Phil-CIA/Development-Station-Power-Supply/NEW_CHAT_HANDOFF.rmd

# Development Station New Chat Handoff

## Session Closeout - 2026-06-21

Project: Development Station Power Supply
Phase: Rev-B PCB review and order-prep gate

## Current Objective

Finish the Rev-B release handoff by checking the Regulator board BOM, then generate fabrication outputs if the BOM is acceptable.

## Why This Session Was Stopped

HAT Rev-B was cleaned up and now has a zero-violation DRC state after the U10 footprint fix. Regulator Rev-B still has only cosmetic DRC warnings, but the BOM on the regulator board must be checked before gerber generation.

## Verified State At Stop

- HAT Rev-B DRC: 0 violations, 0 unconnected pads, 0 footprint errors
- HAT Rev-B ERC: 0 errors, 5 warnings (AHT20/easyeda2kicad library noise only)
- Regulator Rev-B DRC: 2 warnings, 0 unconnected pads, 0 footprint errors
- Connector contract: PASS in both reduced and baseline modes

## Next Session Actions (In Order)

1. Review the Regulator Rev-B BOM before any gerber generation.
2. If BOM is acceptable, generate fabrication outputs for both Rev-B boards.
3. Record artifact paths and timestamps in handoff notes.
4. Keep KERC-04, RB-007, and J21 display power budget deferred for post-order follow-up.

## First Action Next Session

Read `HANDOFF.md`, then review the Regulator Rev-B BOM before generating fabrication outputs.

Date: 2026-06-19
Project: Development Station Power Supply
Phase: Rev-B PCB review and order-prep gate

## Current Objective

Review all recent PCB and schematic deltas across Regulator Rev-B and HAT Rev-B, then determine:
1. Must-fix before order
2. Acceptable-for-order as-is
3. Defer-to-post-order items

## Why This Session Was Stopped

User requested closeout + handoff after successful connector-contract and ERC verification passes.

## Stop Point Summary - What Was Finished

1. `scripts/verify-connector-contract.ps1` updated to match current board connector reality.
2. Required cross-board contract reduced to active design set (10 required mappings).
3. Contract verification passes in both modes:
	- reduced: PASS
	- baseline: PASS
4. Latest ERC/netlist artifacts confirmed present for both Rev-B boards.
5. Root `README.md` updated to reflect current design simplification and board readiness state.

## Verified State At Stop

- HAT Rev-B ERC: 0 errors / 0 warnings
- Regulator Rev-B ERC: 0 errors / 8 warnings (library mismatch warnings only)
- Required connector mappings: 10/10 passing in current script checks

## Files That Matter First

- `HANDOFF.md`
- `README.md`
- `scripts/verify-connector-contract.ps1`
- `hardware/kicad/dsp-regulator-hat-rev-b/DSP-Regulator-HAT-RevB.kicad_sch`
- `hardware/kicad/dsp-regulator-hat-rev-b/DSP-Regulator-HAT-RevB.kicad_pcb`
- `hardware/kicad/dsp-regulator-rev-b/DSP-Regulator-RevB.kicad_sch`
- `hardware/kicad/dsp-regulator-rev-b/DSP-Regulator-RevB.kicad_pcb`

## Next Session Actions (In Order)

1. Open both KiCad projects and run DRC with current fabrication constraints.
2. Build a disposition list for every DRC issue and major manual PCB change:
	- board
	- issue
	- severity
	- decision (fix now / accept / defer)
3. Fix all must-fix items.
4. Re-run DRC and confirm no release-blocking violations.
5. Generate fabrication outputs (gerber, drill, fab notes package).
6. Perform final order readiness review.

## Rules For Next Session

1. Keep current contract baseline intact (J1/J2 mapping and 10 required nets).
2. Do not reintroduce deprecated adjustable-channel connector requirements.
3. Keep scope on PCB release quality; avoid unrelated feature expansion.
4. Preserve verification evidence and timestamps in docs as each gate closes.

## First Action Next Session

Read `HANDOFF.md`, then run DRC on both boards and produce the must-fix/accept/defer table before any new routing edits.

## Suggested Prompt For New Chat

Continue from HANDOFF.md. Review all recent PCB changes on HAT Rev-B and Regulator Rev-B, run DRC on both boards, and produce a must-fix vs acceptable vs defer disposition list. Keep the current connector contract baseline intact and drive to fabrication output readiness.
