Phil-CIA/Development-Station-Power-Supply/NEW_CHAT_HANDOFF_SHORT.rmd

# Development Station Quick Handoff (2026-06-19)

- Session closed by user request for handoff + commit.
- Current source of truth: HANDOFF.md
- Current mission: review all PCB changes and determine must-fix vs acceptable vs defer before order.

What changed in this stop window:
- Connector contract script updated to current board mapping and reduced active signal set.
- Contract checks now pass in both reduced and baseline modes.
- ERC status confirmed:
  - HAT Rev-B: 0 errors, 0 warnings
  - Regulator Rev-B: 0 errors, 8 library warnings
- Root README updated to reflect simplified architecture and order-prep status.

Next session first move:
1. Read HANDOFF.md.
2. Run DRC on both Rev-B boards.
3. Build a disposition list: must-fix / acceptable / defer.

Paste prompt:
Continue from HANDOFF.md. Run DRC on HAT Rev-B and Regulator Rev-B, review all recent PCB edits, and classify issues into must-fix, acceptable, and defer before generating fabrication outputs.
