Phil-CIA/Development-Station-Power-Supply/HANDOFF_2026-05-31.md

# Development Station Power Supply - Handoff (2026-05-31)

## Scope
CrowPanel 4.3 in display + HAT telemetry pipeline stabilization.
Goal was to remove visible flicker while keeping fast live telemetry and usable trend charts.

## Current Baseline (Working)
1. Transport path is UART-only for HAT -> CrowPanel telemetry.
2. Display flicker is eliminated in the current rendering/timing setup.
3. Live value labels are responsive and update quickly.
4. Trend charts are re-enabled and update at a faster decimated cadence.
5. Guarded flash workflow is in use for both targets.

## Firmware State

### HAT (env: hat_c6_i2c_probe)
- File: src/i2c_scanner.cpp
- Telemetry publish loop delay is 100 ms (about 10 Hz source cadence).
- OTA policy flag remains disabled.

### CrowPanel (env: crowpanel43)
- File: crowpanel-43-bringup/include/CrowPanel43Display.h
  - RGB timing tuned for anti-tear baseline:
    - freq_write = 16 MHz
    - vsync_back_porch = 16
- File: crowpanel-43-bringup/src/main.cpp
  - kTrendSampleMs = 200
  - kChartDecimation = 2
  - kUiUpdateMinMs = 50
  - kVoltageUpdateDeadband_mV = 5
  - kCurrentUpdateDeadband_mA = 2
  - Charts enabled, secondary detail UI rate-limited separately
  - OTA policy hard-disabled in code and diagnostics

## What Was Verified
1. Repeated successful builds for HAT and CrowPanel after each tuning step.
2. Guarded flash success on:
   - HAT COM11 (ESP32-C6)
   - CrowPanel COM12 (ESP32-S3)
3. On-device behavior reported by user:
   - No flicker
   - Responsive values
   - Chart speed improved to acceptable state

## Soak Status
1. PASS (user-reported): system has been running for multiple hours with stable behavior.
2. No regressions reported during extended runtime (display stability, value updates, and chart motion remained acceptable).

## Known Pitfall and Recovery
PlatformIO package/install race can occur if multiple runs overlap.
Symptoms include missing framework files or locked firmware artifacts.

Recovery:
1. Stop stale platformio/python processes.
2. Re-run build/upload sequentially (one command at a time).
3. If framework files are missing, recover from .platformio/.cache/tmp/pkg-installing-*.

## Remaining Plan Items
1. Optional fault injection (temporary UART unplug/replug) and behavior notes.
2. Completed: high-level export hardware path planning checklist.

Procedure doc for Items 1-2:
- docs/display-project/SOAK_AND_FAULT_TEST_2026-05-31.md

Export path checklist doc:
- docs/display-project/EXPORT_PATH_CHECKLIST_2026-05-31.md

## Recommended Next Session Start
1. Read this file first.
2. Build and guarded-flash both targets once to confirm clean local state.
3. Run quick bench check:
   - value latency
   - chart motion smoothness
   - no visible flicker
4. Only tune further if user requests additional chart speed.

## Quick Commands
- HAT build: platformio run -e hat_c6_i2c_probe
- HAT flash: powershell -ExecutionPolicy Bypass -File scripts/guarded-flash.ps1 -Target hat -Action upload
- CrowPanel build: platformio run -d crowpanel-43-bringup -e crowpanel43
- CrowPanel flash: powershell -ExecutionPolicy Bypass -File scripts/guarded-flash.ps1 -Target crowpanel -Action upload
