Phil-CIA/Development-Station-Power-Supply/HANDOFF_2026-05-24.md

# WorkStation Handoff - 2026-05-24

## Session Goal
Prepare a clean restart handoff while avoiding conflicts with another active agent in the same repository.

## What Was Updated In This Session
Only these tracked files were intentionally edited in this session:

1. `docs/PROJECT_SPLIT_ISSUES_AND_PRIORITIES.md`
   - Added Issue 12: Rev A display board bring-up as a hard ordering gate.
   - Updated summary tables and redesign sequence to include that gate.

2. `platformio.ini`
   - Added/used ESP32-C6 power-supply environments:
     - `[env:hat_c6_i2c_probe]`
     - `[env:hat_c6_i2c_bridge]`
   - Multiple troubleshooting attempts were made around platform source selection.
   - Current file includes these envs and should be treated as active work-in-progress.

## Current Build Status (Power-Supply Board Path)
Target environment:
- `hat_c6_i2c_probe`

Current state:
- Build is failing.
- Latest observed error chain includes corrupted/locked PlatformIO tool packages and missing toolchain executable in path:
  - `riscv32-esp-elf-g++ is not recognized`
  - package manifest/tools metadata missing during install attempts.

Consequence:
- Upload to COM11 is blocked until PlatformIO package/toolchain state is repaired.

## Important Multi-Agent Coordination
There is another agent actively working in this repo. To avoid stepping on each other:

1. Do not mass-edit or format across the repo.
2. Before changing any file, check ownership in current session notes or chat.
3. Prefer narrow, single-file edits with a short intent note.
4. Avoid touching unrelated modified files shown in `git status`.
5. Treat `src/*.cpp` and `src/*.h` as high-collision areas unless explicitly assigned.

Suggested ownership split for restart:
- Agent A: docs, handoff, planning files (`docs/*.md`, `HANDOFF*.md`).
- Agent B: firmware/tooling execution (`platformio.ini`, `src/*`, build/upload commands).

## Safe Restart Checklist
1. Re-open workspace and run `git status --short` immediately.
2. Confirm who owns `platformio.ini` and `src/*` for this session.
3. If continuing power-supply bring-up, stay on env `hat_c6_i2c_probe` and port COM11.
4. Re-validate toolchain before upload:
   - build first,
   - upload only after successful build.

## Notes
- No commit was created in this session.
- This handoff is intended to preserve continuity without cross-agent merge conflicts.
