Phil-CIA/Development-Station-Power-Supply/HANDOFF_2026-05-27.md

# WorkStation Handoff — May 27, 2026

## Session Overview

Completed full root-cause investigation of near-zero INA3221 current readings on the HAT board. Found and confirmed the definitive hardware defect. Closed out the INA diagnostic work stream and positioned the project for CrowPanel display bring-up next.

---

## What Was Resolved This Session

### Root Cause: NMOS FETs in Wrong Orientation (Q1–Q12)

- Schematic was designed for PMOS (source-high, gate-low = ON).
- Physically installed parts are N-channel (LCSC C22469448, HL3400 clone, Vth ≈ 900mV).
- NMOS source pins connect to +5V_reg → turning on requires Vgate > 5.9V.
- 74HC595 max output = 3.3V → **FETs have never conducted via their channels**.
- The 4.74V drain node reading was body diode equilibrium, not channel conduction.
- **Fix**: Board redesign (planned). No firmware workaround is possible.

### J4 Jumper (non-schematic, must stay)

- Jumper from J4 pin 4 ("Feedback 5V") to J4 pin 7 ("+5V_reg") is the **only** power delivery path to HAT board outputs.
- Removing it without working FETs causes regulator overvoltage (FB pin floats low → duty cycle ramps to max).
- **Leave the jumper installed until the board redesign is complete.**

### INA3221 Status

| Device | Address | Channel | Shunt | Status |
|---|---|---|---|---|
| U1 | 0x40 | CH1 R13 | 200mΩ | Near-zero (FET off + jumper bypass) |
| U1 | 0x40 | CH2 R14 | 200mΩ | Near-zero |
| U2 | 0x41 | CH1 R15 | 200mΩ | Near-zero |
| U2 | 0x41 | CH2 R16 | 200mΩ | Near-zero |
| U2 | 0x41 | CH3 | ~18mΩ empirical | **✅ Working — 12V input monitor ~222mA** |
| U3 | 0x43 | CH1 R17 | 200mΩ | Near-zero |
| U3 | 0x43 | CH2 R18 | 200mΩ | Near-zero |

Only 0x41 CH3 (12V input monitor) gives valid readings. Use it as the only live telemetry source until redesign.

---

## Firmware Left On-Board (HAT)

- Environment: `hat_c6_i2c_probe`, COM11, ESP32-C6 DevKitM-1
- Source: `src/i2c_scanner.cpp`
- State: uploaded and running, scanning INA3221s in a loop
- No changes needed until hardware redesign lands

---

## Next Session Goal: CrowPanel 4.3" Display Bring-Up

The starter target already exists at `crowpanel-43-bringup/`.

### What's Already Done

- PlatformIO env `crowpanel43` targeting `esp32-s3-devkitc-1`
- UART + I2C probe baseline (0x30 board controller, 0x5D touch)
- Full RGB panel pin mapping captured in `include/CrowPanel43Display.h` (LovyanGFX Bus_RGB + GT911 touch)
- Serial command stub: `HELP`, `PING`, `STATUS`, `CMD:LABEL`, `CMD:COLOR`
- RGB panel init intentionally deferred in current baseline

### Bring-Up Plan (Ordered Steps)

**Step 1 — Verify board boots and serial is healthy**
- Build and flash `crowpanel43` env
- Confirm serial output at 115200 baud
- Run `STATUS` command → should respond `board=0x30:ok touch=0x5D:ok`

**Step 2 — Enable RGB panel init**
- Instantiate `CrowPanel43Display` in `main.cpp`
- Call `display.init()` and fill screen with a solid color
- Confirm display lights up (no backlight glitch, correct colors)
- Note: backlight on CrowPanel 4.3 is controlled via the 0x30 board controller over I2C

**Step 3 — Add LVGL layer**
- Add `lvgl` library to `crowpanel-43-bringup/platformio.ini`
- Wire LovyanGFX as the LVGL display driver (flush callback)
- Wire GT911 touch as LVGL input device
- Render a minimal "hello" label to prove the stack end-to-end

**Step 4 — Basic telemetry UI**
- Display live 12V input current (INA3221 0x41 CH3) read over UART from the HAT board
- Lay out a simple bar or numeric widget

### Key Hardware Facts for Next Session

| Item | Value |
|---|---|
| Display | Elecrow CrowPanel Advance 4.3", 800×480 RGB, GT911 touch |
| MCU | ESP32-S3 (on-board) |
| Board controller I2C | 0x30 |
| Touch I2C | 0x5D (GT911) |
| PlatformIO env | `crowpanel43` in `crowpanel-43-bringup/platformio.ini` |
| RGB pixel clock | 21 MHz (freq_write in CrowPanel43Display.h) |
| PSRAM | Required (BOARD_HAS_PSRAM build flag already set) |

### Files to Read First (Next Session)

1. `crowpanel-43-bringup/README.md`
2. `crowpanel-43-bringup/include/CrowPanel43Display.h` — full pin map
3. `crowpanel-43-bringup/src/main.cpp` — current baseline firmware
4. `crowpanel-43-bringup/platformio.ini`
5. `docs/display-project/README.md` — display project context

---

## Session Reference Files

- Full hardware findings: `/memories/repo/hat-board-bringup-findings.md`
- HAT board INA3221 firmware: `src/i2c_scanner.cpp`
- HAT env: `hat_c6_i2c_probe` (COM11, ESP32-C6)
- **Do not use COM4** — that is the separate esp32dev main board

---

## No Commits Created This Session

All changes remain as working files. No git operations were performed.
