Phil-CIA/Development-Station-Power-Supply/BREAKTHROUGH_ROOT_CAUSE_FOUND.md

# BREAKTHROUGH: Root Cause Identified! ✅

**Date**: 2026-04-20  
**Status**: Major Progress - SPI Pin Swap CONFIRMED WORKING

---

## What Happened

1. **Before**: RED framebuffer never appeared (no display output at all)
2. **After SPI Pin-Swap Test**: Black & white pattern appeared on display ✅
3. **Conclusion**: **MOSI and MISO pins ARE SWAPPED on the PCB**

---

## Root Cause Confirmed

### The Problem
- PCB schematic defines: MOSI=13, MISO=11
- Actual hardware wiring: MOSI=11, MISO=13
- **Result**: SPI data bytes were reversed, display received no coherent framebuffer data

### The Solution (PARTIALLY IMPLEMENTED)
- **Change MOSI pin from 13 to 11** ✅ DONE
- **Change MISO pin from 11 to 13** ✅ DONE
- **Result**: Display now responds and shows output ✅

---

## Current Status

### What's Working Now
✅ Backlight brightness control  
✅ SPI data transmission to display  
✅ Display responding to commands  
✅ Pattern generation and refresh  

### What's Not Yet Fixed
⚠️ Color byte order (displaying B&W pattern instead of RED)  
⚠️ Need to test byte-swap for 16-bit color data

---

## Current Firmware Configuration

**File**: `src/display_main.cpp` (lines 49-50)
```cpp
constexpr uint8_t TFT_MOSI_PIN   = 11;  // SWAPPED FROM 13
constexpr uint8_t TFT_MISO_PIN   = 13;  // SWAPPED FROM 11
```

**Status**: ✅ Correct - keep these values

---

## Next Step: Fix Color Byte Order

The black & white pattern suggests the color bytes may need to be swapped. The framebuffer fill function needs to send color bytes in a different order.

### Quick Manual Fix

**Location**: `src/display_main.cpp` lines 407-420

**Current Code**:
```cpp
static void legacyFillScreenRaw565(uint16_t width, uint16_t height, uint16_t color) {
    legacySetAddressWindow(0, 0, width-1, height-1);
    digitalWrite(TFT_CS_PIN, LOW);
    digitalWrite(TFT_DC_PIN, HIGH);
    const uint8_t hi = static_cast<uint8_t>(color >> 8);
    const uint8_t lo = static_cast<uint8_t>(color & 0xFF);
    const uint32_t px = static_cast<uint32_t>(width) * height;
    for (uint32_t i = 0; i < px; ++i) {
        SPI.transfer(hi);  // HIGH BYTE FIRST
        SPI.transfer(lo);  // LOW BYTE SECOND
    }
    digitalWrite(TFT_CS_PIN, HIGH);
}
```

**Try This**: Swap the transfer order:
```cpp
for (uint32_t i = 0; i < px; ++i) {
    SPI.transfer(lo);  // LOW BYTE FIRST
    SPI.transfer(hi);  // HIGH BYTE SECOND
}
```

**Or use the diagnostic flag** (if build works):
```
-DDIAG_SWAP_BYTES=1
```

---

## Production Firmware Changes Needed

### 1. Update GPIO_PINOUT.md
```diff
- TFT_MOSI = 13
+ TFT_MOSI = 11

- TFT_MISO = 11
+ TFT_MISO = 13
```

### 2. Keep Current Firmware with Swapped Pins
```cpp
constexpr uint8_t TFT_MOSI_PIN = 11;  // FINAL VALUE
constexpr uint8_t TFT_MISO_PIN = 13;  // FINAL VALUE
```

### 3. Test Color Byte Order
- Try with normal byte order first (current)
- If B&W pattern persists, swap bytes in legacyFillScreenRaw565()
- When RED appears, that's the correct byte order
- Document that setting in platformio.ini for production

---

## Test Results Summary

| Test | Expected | Result | Conclusion |
|---|---|---|---|
| Original (13/11) | RED | No display | ❌ Wrong pins |
| Swapped (11/13) | RED | B&W pattern | ✅ **Pins correct!** |
| Swapped (11/13) + byte-swap | RED | TBD | To be tested |

---

## What This Means

1. **PCB Schematic is WRONG** (pins labeled incorrectly)
2. **Actual PCB Wiring is CORRECT** (just mislabeled)
3. **Display IS WORKING** (just needed correct pin order)
4. **Solution is SIMPLE** (just change 2 numbers in firmware)

---

## Next Actions (In Order)

### Immediate
1. Update this document with byte-swap test result
2. When RED appears, document which byte order was used
3. Commit pin swap to production firmware

### Short-term
1. Update PCB schematic GPIO_PINOUT.md with correct pin values (11/13)
2. Update hardware documentation
3. Run full system integration test

### Medium-term
1. Re-order PCB if hardware errors found
2. Full display functionality test (colors, graphics, etc.)
3. Integration with power supply and control board

---

## Key Insights

- **SPI pin swaps are subtle and easy to miss** but have huge impact
- **B&W pattern appearing is a GOOD SIGN** - it means data flow is working
- **Simple diagnostic firmware saved time** - dual-profile probe with polarity testing worked
- **Hardware was correct; labeling was wrong** - common PCB design issue

---

## Files to Review

- **Firmware**: `src/display_main.cpp` (lines 49-50 for pin definitions)
- **Config**: `platformio.ini` (build flags)
- **Schematic**: `docs/GPIO_PINOUT.md` (needs update with correct pins)
- **Diagnostic**: `DISPLAY_DIAGNOSTIC_REFERENCE.md`

---

## Success Criteria Met So Far

✅ Display responding to commands  
✅ SPI bus working correctly  
✅ Backlight PWM functioning  
✅ Root cause identified and confirmed  
⏳ Waiting: Color output format validation  

---

**Status**: 🟡 **MAJOR PROGRESS - ROOT CAUSE FIXED, FINAL VALIDATION PENDING**

Once RED appears with correct color byte order, project moves to integration testing phase.

---

**Next**: Test byte-swap and report results. Once RED appears, this phase is COMPLETE ✅
