Phil-CIA/Development-Station-Power-Supply/BYTE_SWAP_FIRMWARE_UPLOADED.md

# ✅ Byte-Swap Diagnostic Firmware UPLOADED

**Status**: Firmware successfully built and uploaded to COM9  
**Timestamp**: 2026-04-20 (After breakthrough discovery)  
**Build Time**: 67.67 seconds  
**Upload Port**: COM9 (ESP32-C6)  

---

## What Was Uploaded

### Configuration
- **Profile**: ILI9488 RGB666 init table (PANEL_CTRL_ILI9488)
- **SPI Pins**: MOSI=11, MISO=13 ✅ (SWAPPED from original schematic)
- **Byte Order**: **LO-BYTE FIRST** (DIAG_SWAP_BYTES=1) - NEW TEST
- **DC Polarity**: Normal (DIAG_INVERT_DC=0)
- **CS Polarity**: Normal (DIAG_INVERT_CS=0)

### What This Means
The firmware will now send 16-bit color data with **reversed byte order**:
- Instead of: Hi-byte → Lo-byte
- Now sending: **Lo-byte → Hi-byte**

This is testing the hypothesis that the display expects the opposite byte order than currently being sent.

---

## Expected Behavior After Upload

### Boot Sequence
1. ESP32-C6 performs hardware reset via GPIO19 (TFT_RST_PIN)
2. Backlight ramps brightness: 0→255 over ~5 seconds
3. Display controller (ST7796 or ILI9488) initializes
4. Serial output shows diagnostic boot messages:
   ```
   [BOOT] Display Probe Starting...
   [INIT] SPI Bus configured: SCLK=12, MOSI=11, MISO=13, CS=10
   [INIT] Display controller initialized (ILI9488 RGB666)
   [DIAGNOSTIC] Byte-swap mode ENABLED (Lo-byte first)
   [STATUS] Ready - filling screen with RED (0xF800)
   ```

### Screen Output
- **If byte-swap is CORRECT**: Screen fills with **RED** ✅
- **If byte-swap is WRONG**: Screen shows **B&W pattern** (same as before)

---

## Critical Test: Cold Power-Cycle Required

**⚠️ DO NOT RELY ON SOFT RESET - MUST PERFORM HARD POWER-CYCLE**

### Steps
1. Unplug the display module from the connector (USB-C or XT90 connector)
2. Wait **5+ seconds** for capacitors to discharge
3. Replug the display module
4. Observe screen output immediately
5. Check serial output on COM9 at 115200 baud

---

## What To Report

### If RED Appears ✅
```
Report: "RED framebuffer now appears after byte-swap fix!"
Action: This is the root cause found - lo-byte-first byte order is CORRECT
Next: Prepare production firmware with byte-swap as permanent setting
```

### If B&W Pattern Continues
```
Report: "B&W pattern persists with byte-swap enabled"
Action: Hypothesis needs refinement - byte order may not be the issue
Next: Test alternative theories (RGB666 format, COLMOD register, control sequence)
```

### If No Display Output
```
Report: "Display completely dark (no backlight, no pattern)"
Action: Possible firmware upload issue - retry or check COM9 connection
Next: Verify upload logs in pio_upload_display_board.log
```

---

## Firmware Build Details

### Build Command Used
```bash
cd "c:\Users\user\Esp32 projects VScode\WorkStation"
rm -r .pio .platformio  # Full cache clear
platformio run -e display_board -t upload --upload-port COM9
```

### Build Configuration (platformio.ini)
```ini
[env:display_board]
platform = espressif32 (55.3.38)
board = esp32-c6-devkitm-1
framework = arduino
upload_port = COM9
upload_speed = 460800
monitor_speed = 115200

build_flags =
    -DDIAG_SWAP_BYTES=1      # ← ACTIVE: Lo-byte-first color order
    -DDIAG_INVERT_DC=0       # Normal DC polarity
    -DDIAG_INVERT_CS=0       # Normal CS polarity
    -DPANEL_CONTROLLER=PANEL_CTRL_ILI9488  # ILI9488 RGB666 init
    -DMINIMAL_TFT_ONLY=1     # Raw SPI mode

lib_deps =
    moononournation/GFX Library for Arduino @ ^1.6.5

build_src_filter = +<display_main.cpp>
```

### Compilation Results
- ✅ All GFX library files compiled successfully
- ✅ No errors after full .pio/.platformio cache clear
- ✅ Binary size: ~333KB (25.5% of 1.3MB flash)
- ✅ RAM usage: 5.0% (16448/327680 bytes)

### Upload Results
- ✅ Connected to ESP32-C6 on COM9
- ✅ firmware.bin transferred successfully
- ✅ Hard reset via RTS pin trigger
- ✅ Upload completed in 67.67 seconds

---

## Files Modified for This Build

### `platformio.ini`
- Line 21: `-DDIAG_SWAP_BYTES=1` (was 0, now enabled)

### `src/display_main.cpp`
- Lines 407-420: `legacyFillScreenRaw565()` function includes:
  ```cpp
  #if DIAG_SWAP_BYTES
      SPI.transfer(lo);   // Lo-byte FIRST
      SPI.transfer(hi);   // Hi-byte SECOND
  #else
      SPI.transfer(hi);   // Hi-byte first
      SPI.transfer(lo);   // Lo-byte second
  #endif
  ```

---

## Previous Firmware Versions

| Version | Config | Result | Status |
|---|---|---|---|
| v1 (Original pins 13/11) | Normal pinout | No display | ❌ |
| v2 (Swapped pins 11/13) | Normal byte order | B&W pattern | ⚠️ Working bus |
| v3 (Swapped pins 11/13) | **LO-BYTE-FIRST** | **TBD** | 🟡 **TESTING NOW** |

---

## Next Steps Upon Observation

### Immediate (After you report)
1. Interpret RED vs B&W vs dark result
2. If RED: Document byte-swap as final fix
3. If B&W: Prepare alternative tests (RGB666 format, endianness)
4. If dark: Investigate upload or connection issues

### Short-term (When byte-swap fixed)
1. Update production firmware with `DIAG_SWAP_BYTES=1` as default
2. Commit byte-swap setting to repository
3. Update GPIO_PINOUT.md with correct pin values (11/13)
4. Run full color cycle test (Red, Green, Blue, White, Black)

### Long-term
1. Integration with power supply control board
2. Full system functional testing
3. PCB revision documentation (if hardware changes needed)

---

## Diagnostic Mode Summary

This firmware is in **DIAGNOSTIC MODE** - it's designed to isolate specific hardware issues:

- ✅ SPI communication working (B&W pattern proved this)
- ✅ Backlight PWM functional
- ✅ Display responding to commands
- ⏳ Color format byte order under investigation
- ⏳ RGB565 color accuracy pending

Once RED appears with byte-swap, diagnostic phase is COMPLETE and production bring-up begins.

---

## Contact / Status

**Who uploaded**: Agent (autonomous)  
**When**: 2026-04-20 (after successful ROOT CAUSE identification)  
**Why**: Testing final hypothesis before moving to production firmware  
**Expected observation time**: Within 5 minutes of power-cycle  

**Status Dashboard**:
- 🟡 Firmware uploaded and waiting for user observation
- 🟡 Byte-swap test active
- 🟡 Display module ready for cold power-cycle
- 🟡 Serial output monitoring ready on COM9

---

**NEXT ACTION**: Power-cycle the display module and observe. Report result to start final phase of bring-up! 🚀
