Phil-CIA/Development-Station-Power-Supply/docs/DEV_STATION_HANDOFF_2026-09-23.md

**AW9523 Bringup Handoff**

Date: 2026-09-23

- **Summary**: Continued bring-up of AW9523 GPIO/LED driver on the Blue Pill helper path. Migrated control to the Adafruit AW9523 driver, enforced GPIO push-pull at boot, added diagnostics and bench commands (including Q9-specific diagnostics), and validated a working build/upload flow using PlatformIO's penv.

- **Changed Files**:
  - **Code**: [stm32-bluepill-bringup/src/main.cpp](stm32-bluepill-bringup/src/main.cpp)
  - **Build**: [stm32-bluepill-bringup/platformio.ini](stm32-bluepill-bringup/platformio.ini)

- **Key Symbols / Routines**:
  - `aw95xxBootInit()` — enforces LEDMODE, GCR push-pull, and `CFG_P0` policy at boot.
  - `aw95xxEnsureGpioPushPull()` — checks/sets GCR and LEDMODE registers.
  - `aw95xxWriteP0Mask()` / `aw95xxSetP0MaskOutputMode()` — set outputs for P0.0/P0.1/P0.5.
  - `Q9DIAG` / `runQ9ElectricalDiagnostic()` — bench diagnostic sequence to detect external clamping on P0.5.

- **How to build & upload (known-good)**:
  - Use PlatformIO penv to avoid host Python 3.14 incompatibility:

    ```powershell
    & "%USERPROFILE%\.platformio\penv\Scripts\platformio.exe" run -d stm32-bluepill-bringup -e bluepill_f103c8
    & "%USERPROFILE%\.platformio\penv\Scripts\platformio.exe" run -d stm32-bluepill-bringup -e bluepill_f103c8 -t upload
    ```

- **Serial/command checks to run in next session** (run from the Blue Pill serial console at 115200):
  - `AWPROBE` — confirm AW9523 ACK at 0x58
  - `AWMODE` — print GCR/CFGs/LEDMODE; expect GCR=push-pull and LEDMODE P0/P1 = 0xFF
  - `Q9DIAG` — run the Q9 diagnostic and capture `aw95xx diag` outputs
  - `Q9ON` / `Q9OFF` — toggle Q9 path and observe `QSTATE` and scope at AW P0.5 and Q9 gate
  - `INANOW` / `INAPROBE` — optional INA readings for rail-state correlation

- **Expected Responses / Bench checks**:
  - `AWMODE` should show: GCR=0x?? (port=push-pull), `LEDMODE_P0`/`P1` = 0xFF, `CFG_P0` = 0xC0 (P0.0..P0.5 outputs)
  - `Q9DIAG` should show `input latch` following output when AW drives high (if external clamp present, diagnostic warns)
  - On oscilloscope: AW P0.5 should actively drive high to ~3.3V when commanded; gate node should move accordingly unless there is a hardware clamp

- **Known issues / notes**:
  - PlatformIO on host Python 3.14 required using the penv executable (documented in repo memory). Do not run `py -m platformio` with system Python 3.14 for library installs.
  - One transient OpenOCD init error occurred during upload historically; retry succeeded. Do not assume intermittent connect failures indicate firmware problems.
  - The code now uses Adafruit AW9523 APIs; avoid mixing manual register writes and library APIs without confirming semantics.

- **Flash safety**: Verify target and COM/adapter before uploading. Do not 'COM port shop' — follow the guarded upload tasks in VS Code tasks.

- **Next actions for the incoming engineer / next chat**:
  - Run the serial checks above and paste the `AWMODE` and `Q9DIAG` outputs into the next chat.
  - If AW P0.5 reads as expected but downstream gate doesn't move, perform powered-off resistance checks and isolate the gate path (measure continuity to ground/3.3V, check diode/clamp parts).
  - If AW doesn't respond at 0x58, check I2C wiring and pull-ups on the board, then run `AWPROBE` and share logs.

Prepared by: Development Station agent — handoff snapshot saved to repo.

---

## Session Scope Update (2026-09-23): Range MOSFET Control

This session is now defined as **range MOSFET control bring-up**.

### Goal

Determine whether firmware has direct command control over MOSFET gate paths and whether the target MOSFET paths respond electrically.

### Added command coverage (Blue Pill AW9523 path)

- `Q1ON` / `Q1OFF` -> AW9523 `P0.2` (`ESP- GPIO 5V Low`) for `Q1/Q7` gate path.
- `Q2ON` / `Q2OFF` -> AW9523 `P0.1` (`ESP- GPIO 5V Hi`) for `Q2/Q8` gate path.
- `Q4ON` / `Q4OFF` -> AW9523 `P0.4` (`ESP- GPIO 3V3 Low`) for `Q4/Q10` gate path.
- `Q5ON` / `Q5OFF` -> AW9523 `P0.3` (`Channel 3 Hi-Range`) for `Q5/Q11` gate path.
- Existing retained:
  - `Q3ON` / `Q3OFF` -> `P0.0` (Q3 path)
  - `Q9ON` / `Q9OFF` -> `P0.5` (Q9 path)
  - `Q39ON` / `Q39OFF` and `Q612ON` / `Q612OFF` pair-level tests

### Recommended bench order for gate-control verification

1. `AWPROBE`
2. `AWMODE`
3. `QSTATE` (baseline capture)
4. `Q1OFF`, `QSTATE`, then `Q1ON`, `QSTATE`, then `Q1OFF`, `QSTATE`
5. `Q2OFF`, `QSTATE`, then `Q2ON`, `QSTATE`, then `Q2OFF`, `QSTATE`
6. Repeat pattern for `Q3`, `Q4`, `Q5`, and `Q9` paths
7. Run `INARAILS` after each ON/OFF transition where current-path response is expected

### What to record per step

- `QSTATE` decode (P0 output bit and direction)
- Scope measurement at AW pin and at MOSFET gate
- INA directional changes when applicable
- Any mismatch where AW output toggles but gate node does not move (possible clamp/loading issue)

---

## Session Closeout (2026-09-23): Range MOSFET Control

### Final verdict

**PASS**: firmware control over the range MOSFET gate paths is confirmed good enough to close this session.

### What was validated live

1. Blue Pill firmware uploaded and verified by ST-Link (`Programming Finished`, `Verified OK`, target reset).
2. AW9523 control path confirmed active at `0x58` (`AWPROBE` ACK).
3. Direct gate-path commands were exercised and read back with matching output and input latch state (`want/out/in` aligned) for:
  - `Q1ON/Q1OFF` -> `P0.2` (`Q1/Q7` path)
  - `Q2ON/Q2OFF` -> `P0.1` (`Q2/Q8` path)
  - `Q3ON/Q3OFF` -> `P0.0`
  - `Q4ON/Q4OFF` -> `P0.4` (`Q4/Q10` path)
  - `Q5ON/Q5OFF` -> `P0.3` (`Q5/Q11` path)
  - `Q9ON/Q9OFF` -> `P0.5`
4. Consolidated OFF->ON->OFF sweep completed for all six paths with `QSTATE` and `INARAILS` captures.
5. Directional INA response observed on expected paths (notably Q2, Q4, Q5), and all paths returned to baseline OFF state (`p0=0x00`) at end of run.

### Closure statement

For current bring-up purposes, this closes the **range MOSFET control** objective. Treat command-path control as validated and move to calibration work in the next session.

---

## Next Session Start: Calibration

Use this as the opening scope for the next chat:

1. Confirm bench baseline (`AWPROBE`, `QSTATE`, `INARAILS`).
2. Keep range paths in known-safe OFF baseline unless a calibration step requires a specific state.
3. Begin calibration sequence (rail/telemetry calibration workflow) and capture coefficients/results.
4. Log final calibration outputs and pass/fail gates in a new handoff entry.
5. Follow `docs/CALIBRATION_WORKFLOW_2026-09-23.md` as the active recovered-and-updated calibration procedure.

Suggested next-session opener text:

"Range MOSFET control session is closed PASS on 2026-09-23. Start calibration session from Blue Pill baseline state with AW9523 verified at 0x58 and all range paths OFF."
