Phil-CIA/Development-Station-Power-Supply/docs/DEV_STATION_HANDOFF_2026-07-29.md

# Dev Station Handoff - 2026-07-29

## Session Closeout

Range-switch driver rework moved from concept to validated schematic/netlist state on HAT Rev-B using LM74502H high-side NMOS drivers.

Primary goal for this session was to resolve the prior ambiguous Vgs behavior on high-side back-to-back NMOS range switches by introducing a proper high-side gate driver topology.

## What Was Completed

1. Implemented LM74502H-based gate drive topology for all four range-switch channels.
2. Confirmed OV divider strategy per channel (R1/R2 style implemented as 390k/100k where shown).
3. Confirmed VCAP charge-pump capacitor presence per channel and net connectivity.
4. Verified U6/U8/U13/U14 channel consistency in netlist (VS, VCAP, GATE, SRC, OV, EN/UVLO).
5. Confirmed ERC export is clean.
6. Created timestamped backup snapshot of key artifacts.

## Verified State At Stop

- HAT Rev-B ERC: 0 errors, 0 warnings.
- Four LM74502H channels pass netlist-level connectivity checks:
  - VS on +5V_Boot
  - VCAP capacitor connected VCAP-to-VS
  - OV divider connected to VS and GND with OV at divider midpoint
  - GATE output isolated from MCU logic nets
  - SRC tied to common source node of each back-to-back NMOS pair
- Backup created at:
  - hardware/kicad/dsp-regulator-hat-rev-b/backups/20260729-042040/
  - includes:
    - DSP-Regulator-HAT-RevB.kicad_sch
    - DSP-Regulator-HAT-RevB.net
    - ERC.rpt

## Important Notes For Next Session

1. Netlist validation is complete; physical layout proximity still matters.
2. Ensure each LM74502H has local VS-to-GND bypass placement close to the IC in PCB layout (in addition to VCAP-to-VS cap).
3. Confirm zener polarity per channel at schematic symbol orientation level:
   - Cathode to gate net
   - Anode to source net

## Open Issue: 5V Reference Headroom

The voltage-reference / selector stage that is supposed to hold the converter in a valid pre-switch state appears to be headroom-limited.

- The stage is being driven from a 5V supply rail.
- A 5V-supplied LMV358-class buffer/comparator cannot guarantee a true 5V high at the output.
- The Schottky combine path adds another forward-drop penalty, so a measured output around 4.3V is consistent with the topology.

Treat this as a topology limitation, not a layout-only defect.

Next check:
- Measure the buffer output and the selector node separately.
- If the converter really needs a 5V-level pre-switch reference, move that source to a rail with headroom or use a rail-to-rail buffer / ideal-diode style selector.

## Recommended Next Actions

1. Do a quick layout pass focused on decoupling and gate-loop geometry around U6/U8/U13/U14.
2. Bench-validate one channel first (EN low/high, OV sweep around expected trip).
3. If channel behavior matches expectation, clone validation across the remaining channels.
4. Start the next problem only after one-channel bench pass confirms stable ON/OFF and clean trip behavior.

## Suggested Next-Chat Startup Prompt

Continue from docs/DEV_STATION_HANDOFF_2026-07-29.md. Assume LM74502H range-switch driver updates are in place for all four channels and netlist/ERC checks are complete. Help me run a focused PCB layout sanity pass, then create a one-channel bench validation checklist with pass/fail criteria before moving to the next issue.
