Phil-CIA/Development-Station-Power-Supply/docs/DEV_STATION_HANDOFF_2026-07-03.md

# Development Station Power Supply - Handoff

## Session Closeout - 2026-07-03

Phase 4 visual polish for CrowPanel is complete and deployed to hardware.
This stop intentionally did **not** begin Phase 5 parameter integration.

## What Was Completed

1. Implemented a 3-screen FNIRSI-inspired UI baseline on CrowPanel:
   - Splash
   - Main telemetry screen
   - Graph/history screen
2. Added demo telemetry mode for showroom behavior without live backend dependency.
3. Added demo tour mode (automatic Main/Graph screen cycling).
4. Applied dark-theme visual calibration toward IPS3608 reference style:
   - yellow voltage accent
   - blue current accent
   - darker neutral panels/status bars
5. Added visual-only fault/limit strip:
   - OVP/OCP/OTP/SCP/LIM
   - COMM WARN when link is stale (non-demo path)
6. Added FNIRSI-style right-side status chips on Main/Graph:
   - OK/WARN
   - M1
   - CV/CC
   - RUN/WAIT
7. Performed multiple guarded flashes to CrowPanel target with successful ESP32-S3 precheck and upload.

## Explicit Scope Boundary (Important)

- Phase 5 (project-specific functionality integration) was deferred by user request.
- No real system parameter binding was added in this session.
- Current advanced indicators are visual-only state representations.

## Current Runtime State

CrowPanel UI remains in visual-prototype mode with demo capabilities:

- `DEMO ON|OFF`
- `TOUR ON|OFF`
- `SCREEN MAIN|GRAPH|SPLASH`
- `SPLASH ON|OFF`
- Existing diagnostics still available (`STATUS`, `RX`, `LOG_*`, `PROBE`).

## Files Modified In This Session

1. `crowpanel-43-bringup/src/main.cpp`
   - screen architecture, style tuning, demo data path, navigation, status chips, visual fault strip

No other source files were required for this stop.

## Build/Flash Status At Close

1. CrowPanel build (`crowpanel43`) passes.
2. Guarded upload for CrowPanel passes when COM12 is available.
3. Device precheck confirms expected chip family (ESP32-S3) and expected port (COM12).

## Known Operational Note

If serial monitor/open-port checks fail with access denied, stale PlatformIO/Python processes may hold COM12.
Resolve by closing monitor tasks/processes before guarded upload.

Additional Windows note from this session:
- If guarded CrowPanel upload crashes during the esptool progress display with a `UnicodeEncodeError` under `cp1252`, run the upload from a UTF-8 console context first:
   - `chcp 65001`
   - `$env:PYTHONIOENCODING='utf-8'`

## Next Session Objective (Phase 5 Start)

Begin project-specific functionality integration on top of this UI.

### Priority Order

1. Define concrete parameter contract to bind into UI:
   - set voltage
   - set current limit
   - output state
   - protection flags
   - measured V/I/P
2. Decide authoritative producer for each parameter (STM32 side vs display-local placeholders).
3. Replace visual-only chip/fault states with real bound states.
4. Add telemetry frame/schema extension only if required by missing fields.
5. Preserve current visual design while wiring real data paths.

### Suggested First Actions

1. Read this handoff and `docs/DEV_STATION_HANDOFF_2026-07-02.md`.
2. Verify current baseline quickly on hardware (`DEMO OFF`, `RX`, `STATUS`).
3. Enumerate required Phase 5 fields and map each to existing telemetry availability.
4. Implement smallest vertical slice first:
   - one real parameter source
   - one visible bound widget
   - verified end-to-end update.

## Definition of Done For Next Session (Phase 5 Slice)

1. At least one UI element currently in visual-only mode is driven by real system data.
2. Guarded build/flash workflow still passes.
3. No regression in screen navigation or render stability.

---

## Continuation Update - 2026-07-03 (Phase 5 Starter Slice)

1. Started Phase 5 with a minimal real-data binding on CrowPanel.
2. Changed runtime default to live telemetry mode:
   - `DEMO` now defaults to OFF at boot.
   - `TOUR` now defaults to OFF at boot.
3. Replaced one static visual-only widget with telemetry-driven behavior:
   - Main-screen status badge now updates as `OUTPUT ON|OFF|??`.
   - `ON` when link is fresh and measured current is above threshold.
   - `OFF` when link is fresh and current is below threshold.
   - `??` when link is stale.
4. Guarded workflow status:
   - CrowPanel build passed.
   - Guarded CrowPanel upload passed with expected COM12 + ESP32-S3 precheck.

### Notes

- This is an interim binding heuristic for output state using measured current until an explicit output-enable/status field is added to the telemetry contract.
- Existing visual style and screen navigation were left intact.

## Continuation Update - 2026-07-03 (Phase 5 Protocol Alignment)

1. Applied the Phase 5 parameter-integration design direction from commit `41a7a08` into live code.
2. Extended the STM32 -> CrowPanel telemetry frame from legacy 10-byte format to an extended frame carrying:
   - CH1 (+5V) voltage/current
   - CH2 (+3.3V) voltage/current
   - temperature
   - status byte
   - protection flags byte
3. CrowPanel UART parser is now backward-compatible:
   - legacy 10-byte frame still accepted
   - extended frame auto-detected by length and parsed when present
4. CrowPanel UI state binding updated to use explicit telemetry fields when available:
   - RUN/WAIT chip uses explicit output-enable bit
   - CV/CC chip uses explicit mode bit
   - fault strip uses explicit protection bits
   - RX diagnostic output now shows CH2, temp, status, protection, and extended-frame presence
5. Deployment status:
   - STM32 Blue Pill build passed
   - STM32 Blue Pill upload passed
   - CrowPanel build passed
   - Guarded CrowPanel upload passed with COM12 + ESP32-S3 precheck

### Current Scope Note

- This is still a transport-and-binding slice, not full Phase 5 completion.
- UI layout remains the Phase 4 visual baseline; the 2-channel IPS3608-style full-screen re-layout is not started yet.

## Continuation Update - 2026-07-03 (Phase 5 Main-Screen Layout Slice)

1. Advanced the CrowPanel Main screen from the old single-rail presentation to a first 2-channel view.
2. Reused the two large main cards as:
   - `CH1 +5V RAIL`
   - `CH2 +3.3V RAIL`
3. Bound both cards to live extended telemetry fields:
   - CH1 voltage/current/power/temperature
   - CH2 voltage/current/power
4. Repurposed the two main bars to show per-channel voltage windows:
   - CH1: 4.5V to 5.5V
   - CH2: 3.0V to 3.6V
5. This is still a transitional Phase 5 layout:
   - graph screen remains mostly Phase 4 style
   - main-screen meta/status area is not yet fully IPS3608-style dual-channel content

### Validation / Hardware State

1. CrowPanel build passed after the layout change.
2. CrowPanel COM12 later re-enumerated normally as `USB-SERIAL CH340K (COM12)`.
3. Guarded CrowPanel upload then passed with expected COM12 + ESP32-S3 precheck.
4. Because strict flash-safety policy is active, no opportunistic port switching was attempted while COM12 was absent.

## Continuation Update - 2026-07-03 (Graph Summary Slice)

1. Updated the Graph screen top summary card to reflect the 2-channel telemetry model.
2. Graph header now shows:
   - CH1 voltage/current summary
   - CH2 voltage/current summary
   - sample count and temperature summary
3. CrowPanel build passed after this follow-up change.
4. Guarded CrowPanel upload also passed after this follow-up change.

## Continuation Update - 2026-07-11 (CrowPanel Layout Cleanup Before Rev B Bench Pivot)

1. Performed a cleanup pass on the CrowPanel Main and Graph screens to reduce visible overflow and clipping seen on hardware photos.
2. Main-screen adjustments in `crowpanel-43-bringup/src/main.cpp`:
   - tightened card text density
   - moved setpoint emphasis into channel headers
   - shortened current and power/status rows
   - retained the right-side chip/status column while making the summary block denser
3. Graph-screen adjustments in `crowpanel-43-bringup/src/main.cpp`:
   - reduced and repositioned the summary card
   - reduced chart widths/heights to avoid overlap with labels and footer regions
   - repositioned the right-side chip column
   - moved the fault row upward to reduce bottom-edge collision
4. Build status for this cleanup pass:
   - Guarded CrowPanel build passed after the layout changes
   - No guarded upload was run in this closeout step
5. Scope note:
   - This was a layout-stability / readability pass, not a final commercial-match polish pass
   - Further visual tuning is still possible later, but is intentionally deferred for now

## Next Session Pivot

1. Pause CrowPanel UI work here.
2. Shift focus to bench power-up of Rev B hardware.
3. Treat the current CrowPanel UI state as a parked prototype baseline unless bench findings require display-side changes.
