Phil-CIA/Development-Station-Power-Supply/docs/DEV_STATION_HANDOFF_2026-07-20.md

# Development Station Power Supply - Handoff

Latest active handoff: [docs/DEV_STATION_HANDOFF_2026-07-20-session2.md](docs/DEV_STATION_HANDOFF_2026-07-20-session2.md)

Previous handoff: [docs/DEV_STATION_HANDOFF_2026-07-14.md](docs/DEV_STATION_HANDOFF_2026-07-14.md)

Session status: superseded by the next 2026-07-20 session handoff.

## Current Session Goal

1. Reestablish communication with the HAT board over the USB path and JTAG pins.
2. Confirm the STM32 Blue Pill bring-up image is still the active baseline.
3. Continue CrowPanel communication work once HAT-side comms are stable.

## Known Good Baseline Entering This Session

1. STM32 Blue Pill firmware was built and flashed successfully over ST-Link.
2. Current firmware includes:
   - `HELP`
   - `FTEST`
   - `AHTNOW`
   - `AHTRESET`
   - `SRTEST`
   - `INAPROBE`
   - `INANOW`
   - `INARAILS`
3. INA3221 bring-up is currently limited to the two remaining HAT devices only:
   - `0x40` = 5V monitor
   - `0x41` = 3.3V monitor + incoming rail monitor
4. `0x43` is not expected on this revision baseline.
5. Firmware currently reports incoming rail data in the 1 Hz heartbeat and the periodic health summary.

## Hardware Baseline at Session Start

1. Regulator board:
   - U5 removed.
   - R15 removed.
   - R28 removed.
   - R9 reinstalled.
   - R10 reinstalled.
   - VSENSE_3V3+ to +3.3V_Reg jumper removed.
   - +5V_Reg to VSENSE_5V+ jumper installed.
2. HAT board:
   - Third INA3221 position U3 removed; only two INA3221 devices remain in this revision baseline.
   - U4 removed.
   - D1 removed.
   - D2 removed.

## Latest Verified Firmware Evidence

1. ST-Link upload and verify passed on the STM32 Blue Pill target.
2. COM7 serial monitor was previously stable at 115200 with recurring heartbeat output.
3. INA command paths were added and flashed, but require live reconnection and validation in this session.

## Immediate Next Steps

1. Reconnect to the HAT-side serial/USB/JTAG path and confirm which interface is live for this bench state.
2. Run `HELP` first to verify the loaded firmware image.
3. Run `INAPROBE` and `INARAILS` to confirm the two-device INA state.
4. Then continue with CrowPanel communication checks.

## Suggested Prompt For New Chat

Continue from the active 2026-07-20 handoff. The STM32 Blue Pill image is already built and flashed, the HAT baseline uses only two INA3221 devices, and the next work is to reestablish communication over the HAT USB/JTAG path and continue CrowPanel communication bring-up.
