Phil-CIA/Development-Station-Power-Supply/docs/DEV_STATION_HANDOFF_2026-05-24.md

DEV STATION CLOSEOUT START

Date: 2026-05-24
Project: Development Station Power Supply
Phase: PCB revision

What Was Completed Today:
1. Connector verification flow stabilized: reduced mode passes after net-name normalization and verifier hardening.
2. Rev-B schematic label cleanup completed for leading-space global labels and both Rev-B netlists were re-exported.
3. Blue Pill migration cleanup completed for active HAT U7 symbol identity (legacy Espressif lib_id replaced with local Blue Pill migrated symbol identity).
4. Issue tracker and redesign prep docs were updated to isolate one remaining migration blocker (KERC-04 reset-safe startup bench evidence).
5. KERC-04 bench runbook and handoff-ready evidence template were created.

What Changed:
- Files updated:
  - scripts/verify-connector-contract.ps1
  - hardware/kicad/dsp-regulator-rev-b/DSP-Regulator-RevB.kicad_sch
  - hardware/kicad/dsp-regulator-hat-rev-b/DSP-Regulator-HAT-RevB.kicad_sch
  - hardware/kicad/dsp-regulator-rev-b/DSP-Regulator-RevB.net
  - hardware/kicad/dsp-regulator-hat-rev-b/DSP-Regulator-HAT-RevB.net
  - hardware/kicad/dsp-regulator-hat/DSP Regulator_hat.kicad_sch
  - docs/PROJECT_SPLIT_ISSUES_AND_PRIORITIES.md
  - docs/PCB_REDESIGN_PREP_2026-05-20.md
  - docs/KERC-04_RESET_STARTUP_VALIDATION.md
- Behavior changed:
  - verify-connector-contract supports baseline policy mode switch:
    - default baseline policy: reduced-policy (informational feedback crossings)
    - strict baseline policy: explicit feedback-crossing enforcement
- Hardware changes: none (documentation/schematic/netlist updates only)
- Bench evidence captured: no

Current State At Stop:
- Current active target: Blue Pill migration closure gate (Issue 15, KERC-04)
- Current highest-risk unresolved item: reset-safe startup behavior for ISET_MPU_5V / ISET_MPU_3V3 / ISET_MPU_Channel_3 not yet bench-captured
- Safe resume point: run KERC-04 scope captures per docs/KERC-04_RESET_STARTUP_VALIDATION.md and record pass/fail table
- Hardware left connected: unknown (not modified in this session)

Bench Deferral Note:
- KERC-04 bench capture is intentionally deferred to next bench-available session (target: 2026-05-25).
- No additional schematic or verifier edits are pending before this capture.

Memory Pool Update (60 Seconds):
- active-baseline.md: no change
- decision-log.md: no change
- open-loops.md: KERC-04 remains final hold for Issue 15
- bench-log.md: no new bench data
- development-station-power-supply.md: updated with connector gate closure, symbol identity normalization, and KERC-04 runbook addition

Known-Good Checks:
1. powershell -ExecutionPolicy Bypass -File scripts/verify-connector-contract.ps1 -RegulatorNetlist "hardware/kicad/dsp-regulator-rev-b/DSP-Regulator-RevB.net" -HatNetlist "hardware/kicad/dsp-regulator-hat-rev-b/DSP-Regulator-HAT-RevB.net" -Mode reduced -> PASS
2. powershell -ExecutionPolicy Bypass -File scripts/verify-connector-contract.ps1 -RegulatorNetlist "hardware/kicad/dsp-regulator-rev-b/DSP-Regulator-RevB.net" -HatNetlist "hardware/kicad/dsp-regulator-hat-rev-b/DSP-Regulator-HAT-RevB.net" -Mode baseline -> PASS (default reduced-policy)
3. powershell -ExecutionPolicy Bypass -File scripts/verify-connector-contract.ps1 -RegulatorNetlist "hardware/kicad/dsp-regulator-rev-b/DSP-Regulator-RevB.net" -HatNetlist "hardware/kicad/dsp-regulator-hat-rev-b/DSP-Regulator-HAT-RevB.net" -Mode baseline -BaselineFeedbackPolicy strict -> expected FAIL (3 feedback crossings)

Still Blocked By:
1. KERC-04 bench evidence not yet captured
2. No scope captures yet attached to handoff for startup/reset proof

Source Of Truth Files:
- HANDOFF.md
- NEW_CHAT_HANDOFF.rmd
- docs/GPIO_PINOUT.md
- docs/USB_HUB_CHANGE_TRACKER.md
- docs/PROJECT_SPLIT_ISSUES_AND_PRIORITIES.md
- docs/PCB_REDESIGN_PREP_2026-05-20.md
- docs/KERC-04_RESET_STARTUP_VALIDATION.md
- hardware/kicad/dsp-regulator-hat/DSP Regulator_hat.kicad_sch

Next Session Priority Order:
1. Execute KERC-04 scope captures (power-on, reset, optional brownout)
2. Fill KERC-04 evidence table and add capture filenames to this handoff
3. Promote KERC-04 to PASS if all runs meet criteria; otherwise log mitigation and retest plan

First Action Next Session:
- Open docs/KERC-04_RESET_STARTUP_VALIDATION.md and run R1 power-on single-shot capture with CH1=NRST and CH2/3/4 on ISET lines.

Tomorrow Quick-Start Checklist:
1. Open docs/KERC-04_RESET_STARTUP_VALIDATION.md.
2. Set scope channels CH1..CH4 exactly as listed in that runbook.
3. Capture R1 (power-on), R2 (manual reset), R3 (brownout optional).
4. Paste results into this handoff using the runbook template section.
5. Mark KERC-04 PASS/HOLD with one-sentence rationale.

Instructions For Next Chat:
1. Read this handoff first.
2. Read /memories/repo/index.md, then active-baseline.md and open-loops.md.
3. Do not reopen connector-contract edits unless new failures appear.
4. Focus only on KERC-04 validation until PASS/HOLD decision is evidenced.
5. Append exact waveform filenames and pass/fail decisions to this handoff.

Session Closeout Status:
- This session is closed by user request.
- Current effort is parked with KERC-04 intentionally open pending bench availability.
- Next effort should start in a new chat after reviewing this handoff.

DEV STATION CLOSEOUT END
