Phil-CIA/Development-Station-Power-Supply/docs/DEV_STATION_HANDOFF_2026-05-25.md

DEV STATION CLOSEOUT START

Date: 2026-05-25
Project: Development Station Power Supply
Phase: PCB revision (Rev-B HAT MCU migration)

What Was Completed Today:
1. Continued Rev-B HAT U9 migration and normalized legacy debug/boot labels to STM32-style names.
2. Added conservative debug/program access infrastructure (SWDIO/SWDCLK/NRST labels and six new test points for UART/SWD/NRST/BOOT0).
3. Updated migration tracking documentation and validated edited files are syntax-clean.

What Changed:
- Files updated:
  - HANDOFF.md
  - NEW_CHAT_HANDOFF.rmd
  - NEW_CHAT_HANDOFF_SHORT.rmd
  - docs/STM32_BLUEPILL_PIN_TABLE.md
  - hardware/kicad/dsp-regulator-hat-rev-b/DSP-Regulator-HAT-RevB.kicad_sch
  - docs/DEV_STATION_HANDOFF_2026-05-25.md
- Behavior changed:
  - Rev-B HAT schematic now exposes UART/SWD/NRST/BOOT0 through explicit test access points for controlled bring-up.
- Hardware changes:
  - Schematic-level changes only (no physical bench rewiring recorded in this session).
- Bench evidence captured:
  - no

Current State At Stop:
- Current active target: safe closure of Rev-B U9 migration pin ownership and reset/boot behavior.
- Current highest-risk unresolved item: incomplete U9 pin-name versus net-ownership reconciliation can still cause semantic mismatch.
- Safe resume point: perform explicit U9 pin-by-pin reconciliation first, then finalize BOOT0 default strap and NRST deterministic reset network.
- Hardware left connected: unknown (no bench actions run in this session).

Memory Pool Update (60 Seconds):
- active-baseline.md: no change
- decision-log.md: no change
- open-loops.md: added Rev-B MCU migration risk note about U9 pin reconciliation before final BOOT0/NRST closure
- bench-log.md: no change
- development-station-power-supply.md: no change

Known-Good Checks:
1. get_errors on hardware/kicad/dsp-regulator-hat-rev-b/DSP-Regulator-HAT-RevB.kicad_sch -> no errors
2. get_errors on docs/STM32_BLUEPILL_PIN_TABLE.md -> no errors
3. New handoff set refreshed and aligned for clean next-session restart

Still Blocked By:
1. U9 full pin-number to net-ownership reconciliation not yet complete
2. Final BOOT0 default-low resistor and deterministic NRST network still pending

Source Of Truth Files:
- HANDOFF.md
- NEW_CHAT_HANDOFF.rmd
- NEW_CHAT_HANDOFF_SHORT.rmd
- docs/STM32_BLUEPILL_PIN_TABLE.md
- hardware/kicad/dsp-regulator-hat-rev-b/DSP-Regulator-HAT-RevB.kicad_sch

Next Session Priority Order:
1. Build and verify an explicit U9 pin map from current schematic wiring.
2. Resolve any mismatches and finalize BOOT0/NRST hardware behavior.
3. Re-export netlist and run connector verification checks with recorded evidence.

First Action Next Session:
- Open HANDOFF.md, NEW_CHAT_HANDOFF.rmd, and docs/STM32_BLUEPILL_PIN_TABLE.md, then start U9 pin-by-pin reconciliation in the Rev-B HAT schematic.

Instructions For Next Chat:
1. Read the handoff docs first.
2. Read /memories/repo/index.md, then active-baseline.md and open-loops.md before new changes.
3. Keep scope on Rev-B U9 migration closure only.
4. Use one focused schematic change set at a time, then validate immediately.
5. Record exact verification command outcomes after netlist re-export.

Session Closeout Status:
- Session intentionally closed by user request.
- Work is parked at a clean restart boundary with handoff docs updated.

DEV STATION CLOSEOUT END
