Phil-CIA/Development-Station-Power-Supply/docs/DEV_STATION_HANDOFF_2026-05-18.md

# Development Station Handoff (2026-05-18)

Purpose: clean restart handoff for the next chat with hardware revision work as the active priority.

## Session Intent And Stop Call

- User requested a handoff restart.
- Scope is regulator/HAT Rev-B schematic and netlist work.
- Firmware feature work stays paused.
- Bench execution stays deferred unless explicitly requested.

## What Was Completed

1. Re-verified fresh Rev-B regulator and HAT netlists after schematic updates.
2. Corrected Sense-B source mapping to HAT Rev-B netlist and verified:
   - 5V via R59/R60
   - 3.3V via R61/R62
   - Adj via R63/R64
3. Verified RB-001 implementation across all three channels in regulator Rev-B netlist:
   - U5/U6/U7 = LMV358IDR
   - D4/D5/D6 = BAT54C common-cathode combine
   - R31/R33/R35 = 100 ohm local-input series
   - R32/R34/R36 = 33k local attenuation to GND
4. Locked design intent: remote-primary sensing plus slightly underbiased local fallback to minimize handoff step while preserving startup fallback.

## Current State At Stop

- Hardware status: 3-channel selector topology is implemented and netlist-verified.
- Closure status: bench bring-up validation is still required to confirm continuity/step behavior.
- Documentation status: handoff files were restarted to remove stale mixed-context guidance.

## Risks And Guardrails

1. Do not run bench steps unless explicitly requested.
2. Do not change topology before tracker wording is synchronized to current intent.
3. Keep firmware edits out of scope unless required, and then limit to src/rev1 only.

## Source Of Truth Files

- HANDOFF.md
- NEW_CHAT_HANDOFF.rmd
- NEW_CHAT_HANDOFF_SHORT.rmd
- docs/DEV_STATION_HANDOFF_2026-05-18.md

## Priority Order For Next Session

1. Align issue-tracker wording with remote-primary plus underbiased-local fallback behavior.
2. Preserve current 3-channel implementation unless bring-up data requires resistor retune.
3. Capture each hardware delta in handoff docs before stop.

## First Action Next Session

Read HANDOFF.md and NEW_CHAT_HANDOFF.rmd, then verify latest Rev-B netlist still contains U5/U6/U7, D4/D5/D6, and R31-R36 values before further edits.

## Suggested New Chat Prompt

Continue Development Station hardware revision work from HANDOFF.md and NEW_CHAT_HANDOFF.rmd. Keep scope on regulator/HAT Rev-B schematic and netlist updates only. Preserve the current 3-channel LMV358 plus BAT54C selector topology unless bring-up data drives value changes. Do not run bench steps unless explicitly requested. Keep firmware paused unless absolutely required, and if needed, edit only src/rev1 files.
