Phil-CIA/Development-Station-Power-Supply/docs/DEV_STATION_HANDOFF_2026-05-19.md

# Development Station Handoff (2026-05-19)

Purpose: carry forward today's schematic-first checkpoint with explicit firmware freeze and verified Rev-B netlist evidence.

## Session Intent And Stop Call

- Continue from the new handoff chain and stabilize documentation consistency.
- Keep active scope on regulator/HAT Rev-B schematic and netlist population.
- Keep firmware in scaffold-only mode for inversion/bring-up support.
- Keep bench execution deferred unless explicitly requested.

## What Was Completed

1. Updated handoff chain to consistently describe scaffold-only firmware status:
   - HANDOFF.md
   - NEW_CHAT_HANDOFF.rmd
   - NEW_CHAT_HANDOFF_SHORT.rmd
2. Aligned RB-001 issue tracker wording to current reality:
   - topology implemented and netlist-verified
   - remaining work is bring-up validation and potential value retune
3. Ran strict text verification pass on current Rev-B netlists and recorded a checkpoint in HANDOFF.md.

## Verified Evidence (Today)

Regulator Rev-B netlist:
- U5/U6/U7 present with LMV358IDR values
- D4/D5/D6 present with BAT54C,215 values
- R31/R33/R35 = 100 ohm
- R32/R34/R36 = 33k

HAT Rev-B netlist:
- Sense-B resistor groups present:
  - 5V: R59/R60
  - 3.3V: R61/R62
  - Adj: R63/R64
- Sense nets present:
  - VSENSE_5V+/VSENSE_5V-
  - VSENSE_3V3+/VSENSE_3V3-
  - VSENSE_ADJ+/VSENSE_ADJ-
- Feedback nets present:
  - Feedback 5V
  - Feedback 3.3
  - Feedback Adj Channel

## Current State At Stop

- Hardware status: Rev-B selector topology is present in current netlists.
- Documentation status: tracker and handoff wording are aligned with current implementation state.
- Firmware status: scaffold-only freeze remains active.

## Risks And Guardrails

1. Do not introduce new topology changes before explicit bring-up evidence requires one.
2. Do not expand firmware behavior while schematic/netlist population remains primary.
3. If firmware is touched for blocker resolution, constrain to src/rev1 only and keep change minimal.

## Source Of Truth Files

- HANDOFF.md
- NEW_CHAT_HANDOFF.rmd
- NEW_CHAT_HANDOFF_SHORT.rmd
- docs/PROJECT_SPLIT_ISSUES_AND_PRIORITIES.md
- docs/DEV_STATION_HANDOFF_2026-05-19.md

## Priority Order Next Session

1. Continue schematic/netlist population while preserving current 3-channel topology baseline.
2. Capture each schematic/netlist delta in handoff docs at stop points.
3. Only after explicit request, execute bring-up measurements for continuity/step behavior.

## First Action Next Session

Read HANDOFF.md and this file, then verify U5/U6/U7, D4/D5/D6, and R31-R36 are still present in the latest Rev-B netlist before any further topology edits.

## Suggested New Chat Prompt

Continue Development Station hardware revision work from HANDOFF.md and docs/DEV_STATION_HANDOFF_2026-05-19.md. Keep scope on regulator/HAT Rev-B schematic and netlist updates only. Preserve the current 3-channel LMV358 plus BAT54C selector topology unless bring-up data requires value retuning. Keep firmware in scaffold-only freeze mode unless a schematic-driven blocker requires a narrow src/rev1 update.

## Batch Execution Record (2026-05-19)

Batch ID: B1 (verification-only, no schematic edits)

Checks executed:
1. Regulator netlist component presence and values:
  - U5/U6/U7 with LMV358IDR
  - D4/D5/D6 with BAT54C,215
  - R31/R33/R35 = 100 ohm
  - R32/R34/R36 = 33k
2. HAT netlist mapping presence:
  - R59/R60, R61/R62, R63/R64
  - VSENSE_5V+/-, VSENSE_3V3+/-, VSENSE_ADJ+/-
  - Feedback 5V, Feedback 3.3, Feedback Adj Channel

Result: PASS

Notes:
- No baseline reference loss detected.
- No topology changes introduced in this batch.
- Next batch should be a single focused schematic edit group followed by immediate netlist re-export and targeted verification.

Batch ID: B2 (RB-003 control-path pre-edit verification)

Checks executed:
1. Verified ON/OFF drain-net mapping:
  - U2 pin 5 on Net-(Q2-D)
  - U4 pin 5 on Net-(Q3-D)
  - U3 pin 5 on Net-(Q16-D)
2. Verified channel-select inputs into gate networks:
  - ISET_MPU_Channel_3 -> R63 -> Net-(Q2-G)
  - ISET_MPU_5V -> R24 -> Net-(Q3-G)
  - ISET_MPU_3V3 -> R2 -> Net-(Q16-G)
3. Verified default pulls are present in each path:
  - ON/OFF pulls: R65, R5, R1 to +5V_Boot
  - Gate pulls: R64, R4, R6 to GND

Result: PASS (for one-to-one pin-5 drain mapping and input/pull presence)

Finding recorded:
- Current export shows Q2/Q3/Q16 source pins on GND; prior wording that referenced source-specific `Net-(Qx-S)` ties to +12V was stale and has been corrected in PROJECT_SPLIT_ISSUES_AND_PRIORITIES.md.

Batch ID: B3 (RB-003 pull-value baseline verification)

Checks executed:
1. Verified ON/OFF pull resistor values:
   - R1 actual value in export: 10kΩ (documented as "100k")
   - R5 actual value in export: 10kΩ (documented as "100k")
   - R65 actual value in export: 10kΩ (documented as "100k")
2. Verified gate-drive pull resistor values:
   - R4 = 100kΩ (matches documented)
   - R6 = 100kΩ (matches documented)
   - R24 = 100kΩ (matches documented)
   - R64 = 100kΩ (matches documented)

Result: CRITICAL MISMATCH FOUND

Finding: ON/OFF pull values are 10k in current export, not 100k as stated in PROJECT_SPLIT_ISSUES_AND_PRIORITIES.md issue tracker wording.

Impact and next action: 
- This affects cold-start charge time for ON/OFF nodes.
- Documentation in PROJECT_SPLIT_ISSUES_AND_PRIORITIES.md must be corrected to state R1/R5/R65 = 10k.
- Batch 3 has NOT introduced any schematic changes; this is a pre-edit baseline discovery that prevents future misalignment.

Batch ID: B4 (Rev-B control-label cleanup)

Checks executed:
1. Normalized schematic global labels:
  - ISET_MPU_3V3
  - ISET_MPU_Channel_3
2. Synced the Rev-B netlist text to remove the same leading-space label names.

Result: PASS

Notes:
- The KiCad CLI was not available in this environment, so the netlist file was brought back into sync directly after the schematic edit.
- No topology changes were introduced; this was a label-cleanup batch only.
