Phil-CIA/Development-Station-Power-Supply/docs/DEV_STATION_HANDOFF_2026-05-23.md

# Development Station Handoff (2026-05-23)

DEV STATION CLOSEOUT START

Date: 2026-05-23
Project: Development Station Power Supply
Phase: PCB revision

What Was Completed Today:
1. Locked both inter-board connectors to identical Samtec pairs: CLP-110-02-L-D with FW-10-05-L-D-400-150-A (2 connector pairs total, 40 positions).
2. Updated active capacity baseline to 3.1 A/contact nominal and 2.17 A/contact derated (70%), with current snapshot 18 signal positions + three 3.0 A rails and provisional usage 29 used / 11 spare.
3. Corrected allocation policy to mixed distribution across both connectors and added an SMT placement study gate (A/B/C variants, hard gates, scoring matrix) before pin freeze.

What Changed:
- Files updated: docs/PCB_REDESIGN_PREP_2026-05-20.md, docs/DEV_STATION_HANDOFF_2026-05-23.md, /memories/repo/development-station-power-supply.md
- Behavior changed: connector planning now assumes mixed net distribution across both SMT connectors; no strict power-vs-control split.
- Hardware changes: none in this session.
- Bench evidence captured: no; documentation and planning updates only.

Current State At Stop:
- Current active target: connector planning closure and placement-readiness gate definition.
- Current highest-risk unresolved item: real on-board SMT placement quality (escape routing, access, and robustness) is not yet validated in PCB layout.
- Safe resume point: run SMT placement variants A/B/C in KiCad, score them, and freeze placement before final pin-number mapping.
- Hardware left connected: no bench changes in this session.

Memory Pool Update (60 Seconds):
- active-baseline.md: no change
- decision-log.md: no change
- open-loops.md: no change
- bench-log.md: no change
- development-station-power-supply.md: added durable note that both connectors are locked to identical CLP/FW pairs with mixed distribution policy and next-session focus on ESP32-C6 to STM32 Blue Pill migration.

Known-Good Checks:
1. Both connector roles are now locked to the same Samtec CLP/FW pair family and part numbers.
2. The 40-position model and 18-signal/3x3A snapshot are documented with derived usage/spare counts.
3. Mixed-distribution policy and SMT placement gate are documented before pin freeze.

Still Blocked By:
1. Datasheet evidence fields still need direct source citation capture.
2. SMT placement variants are not yet executed/scored in KiCad.

Source Of Truth Files:
- HANDOFF.md
- NEW_CHAT_HANDOFF.rmd
- docs/GPIO_PINOUT.md
- docs/USB_HUB_CHANGE_TRACKER.md
- docs/PCB_REDESIGN_PREP_2026-05-20.md

Next Session Priority Order:
1. Start MCU migration planning from ESP32-C6 to STM32 Blue Pill.
2. Build migration impact map (rails/logic levels, boot/program/debug path, interface remaps).
3. Create initial schematic plus firmware migration checklist with blockers.

First Action Next Session:
- Open docs/PCB_REDESIGN_PREP_2026-05-20.md and add section "ESP32-C6 to STM32 Blue Pill Migration Baseline" with interface remap and voltage-compatibility checks.

Instructions For Next Chat:
1. Read the handoff docs first.
2. Read /memories/repo/index.md, then active-baseline.md and open-loops.md before new changes.
3. Stay on the current target until the blocking validation step is resolved.
4. Prefer one focused test or one focused code change at a time.
5. Preserve known-good checkpoints and note exact commands when they matter.

DEV STATION CLOSEOUT END
