Phil-CIA/Development-Station-Power-Supply/docs/DEV_STATION_HANDOFF_2026-05-21.md

# Development Station Handoff (2026-05-21)

Purpose: close out PCB-prep decisions for today and leave a clean pre-order checklist for Rev-C.

## Session Intent And Stop Call

- Close decision gaps that blocked pre-order readiness.
- Convert footprint verification into a required measurement gate before ordering.
- Sync handoff and planning docs so next session can execute remaining blockers directly.

---

## What Was Completed

1. Locked schematic policy decisions for Rev-C planning:
   - D9/D10/D11 remain footprinted and default DNP for first Rev-C build.
   - Unused comparator channels are parked deterministically (+IN/-IN to GND, outputs off fault bus).
   - Bootstrap naming is locked to a single +5V_Boot cross-board contract.

2. Added a required Footprint Measurement Gate before board order:
   - Datasheet-vs-footprint geometry check is now mandatory.
   - Measurement table added for changed footprints (pitch/body/pad/courtyard and PASS/FAIL).

3. Updated pre-order issue triage so blockers are explicit:
   - RB-005 includes footprint confirmation plus measured-dimension logging.
   - Remaining blockers are now mechanical fit, footprint verification, and conditional continuity check.

4. Updated checklist flow in redesign prep:
   - Added a checkbox to complete footprint measurement records before netlist/Gerber release.

---

## Current State At Stop

- Active target: Rev-C pre-order readiness documentation and blocker closure.
- Highest-risk unresolved item: physical measurement completion (footprint and stack-height data) before order release.
- Safe resume point: run the Footprint Measurement Gate and fill measured values for the changed footprint(s), then complete stack/enclosure measurements.
- Hardware left connected: no bench changes in this session (documentation and planning updates only).

---

## Known-Good Checks

1. Schematic policy decisions are now documented as locked in the handoff and redesign prep docs.
2. Pre-order triage contains explicit blocker ownership and timing for RB-005 and RB-007.
3. Footprint measurement is now written as a required gate, not a suggestion.

---

## Still Blocked By

1. Footprint measurement values not yet recorded for the changed footprint(s) (RB-005 closure pending).
2. Regulator/HAT stack-height and enclosure-fit measurements not yet captured (RB-007 closure pending).
3. Adjustable rail feedback continuity check still pending (Issue 11 conditional blocker).

---

## Source Of Truth Files

- docs/DEV_STATION_HANDOFF_2026-05-21.md (this file)
- docs/DEV_STATION_HANDOFF_2026-05-20.md (prior detailed technical baseline)
- docs/PCB_REDESIGN_PREP_2026-05-20.md (pre-order triage, measurement gate, action checklist)
- docs/PROJECT_SPLIT_ISSUES_AND_PRIORITIES.md (master issue tracker)

---

## Next Session Priority Order

1. Complete Footprint Measurement Gate entries for changed footprint(s), including PASS/FAIL.
2. Measure board stack height and compare against enclosure budget.
3. Run adjustable-rail feedback continuity quick-check and clear/promote Issue 11.
4. Re-export netlists after measurement and continuity closures.

## First Action Next Session

- Open docs/PCB_REDESIGN_PREP_2026-05-20.md and fill the Footprint Measurement Gate table for the changed footprint before any order-release action.

---

## Instructions For Next Chat

1. Read this handoff file first.
2. Read memories in this order: /memories/repo/index.md, /memories/repo/active-baseline.md, /memories/repo/open-loops.md.
3. Treat measurement completion as required release criteria, not optional notes.
4. Keep bench bring-up deferred unless a blocker requires electrical verification.
