Phil-CIA/Development-Station-Power-Supply/docs/display-project/crowpanel-screens-tracker.md

# CrowPanel Screens & UX Tracker

Coordination doc for the "make the CrowPanel feel like a real product" work.
This file is the source of truth for status across sessions. Update it in each
merged PR so the next session can rebase / continue cleanly.

- Scope target: `crowpanel-43-bringup/` (ESP32-S3, LVGL, UDI UART to STM32 HAT)
- Coordination: this tracker lives on `main` after its documentation PR merges.
- Related issues: #26 (crowpanel display screens), #27 (Bootup log and testing),
  #37 (ESP32 startup test), #38 (SPI memory test), #39 (I2C startup test),
  #40 (CrowPanel startup test)
- Related spec: `docs/DISPLAY_INTERFACE_STANDARD.md` (UDI)

## Rules of engagement

- One branch per bucket, all branched off `main` (not off this branch).
- One PR per bucket, small and reviewable, bench-tested on the physical CrowPanel.
- Never commit to `main` directly (see `docs/SYSTEM_DEVELOPMENT_WORKFLOW.md`).
- Do **not** stack D2–D8 on this branch. The audit doc lives here; behavior work
  starts fresh off `main` after this tracker PR merges.
- No new root-level HANDOFF/SUMMARY files. Update this tracker instead.
- All host↔display messaging must conform to the UDI framing
  (`CMD:` / `ACK:` / `EVT:` / `ERR:`).
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
