Phil-CIA/Development-Station-Power-Supply/docs/display-project/screenshots/audit/setup.jpeg

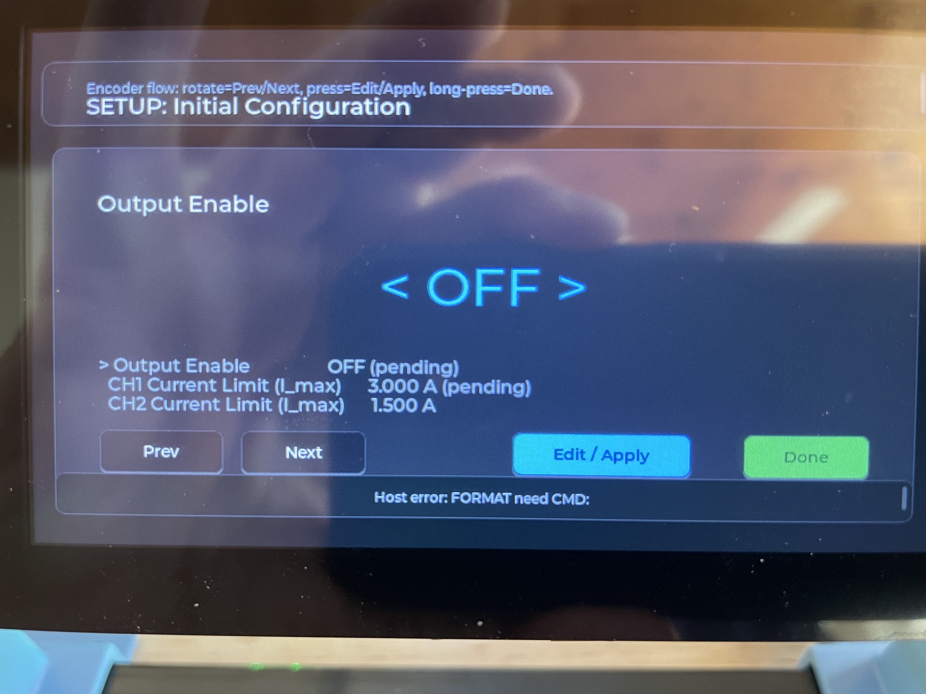
docs/display-project/screenshots/audit/setup.jpeg
