Phil-CIA/Development-Station-Power-Supply/docs/display-project/screenshots/audit/graph-before-fix.jpeg

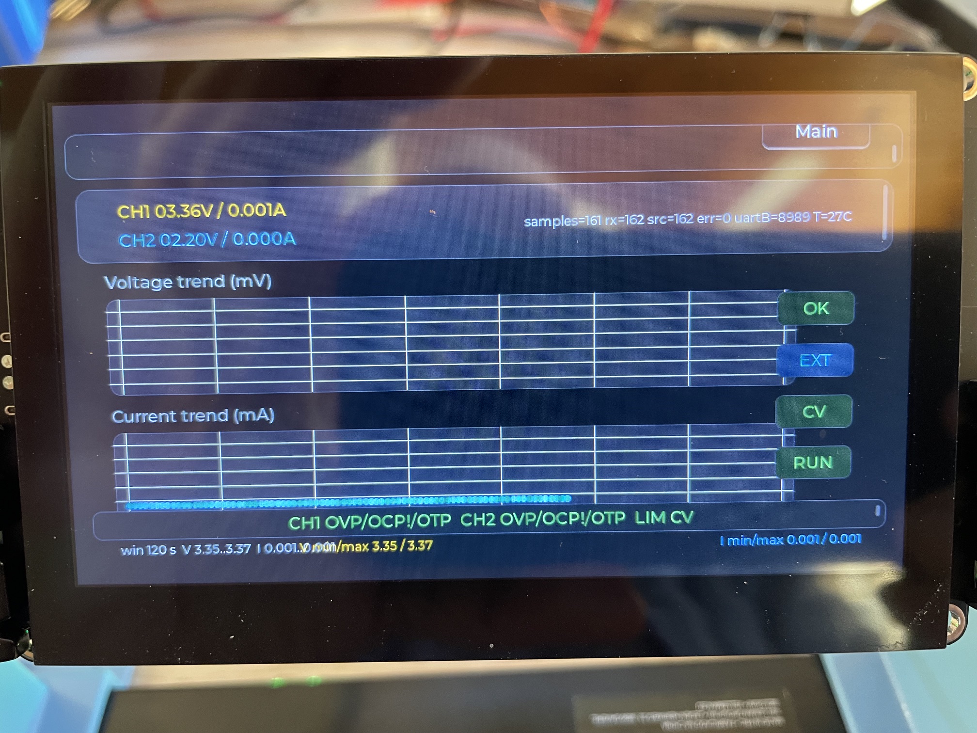
docs/display-project/screenshots/audit/graph-before-fix.jpeg
